ryu10/sbc6802/graphics/sbc6802r2-a.png

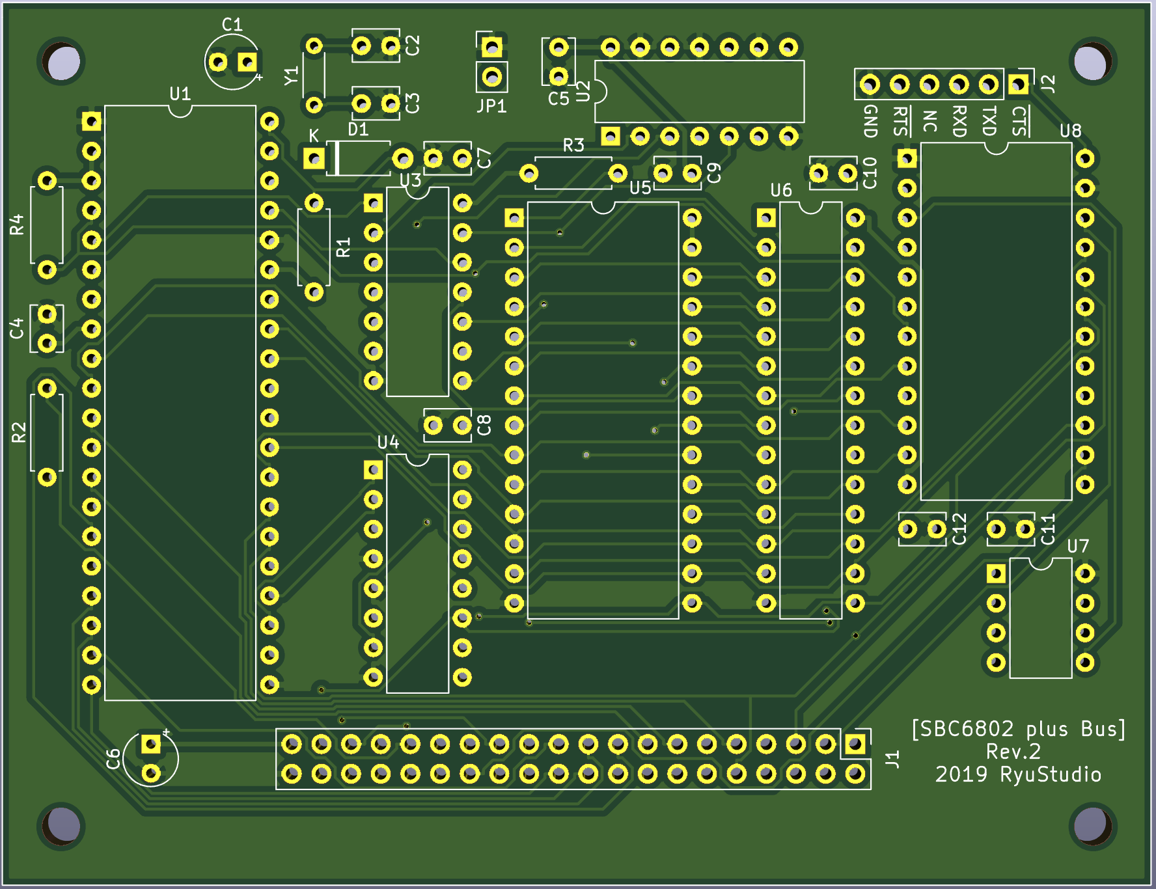
graphics/sbc6802r2-a.png
