ryu10/sbc6802/graphics/sbc6802r2-b.png

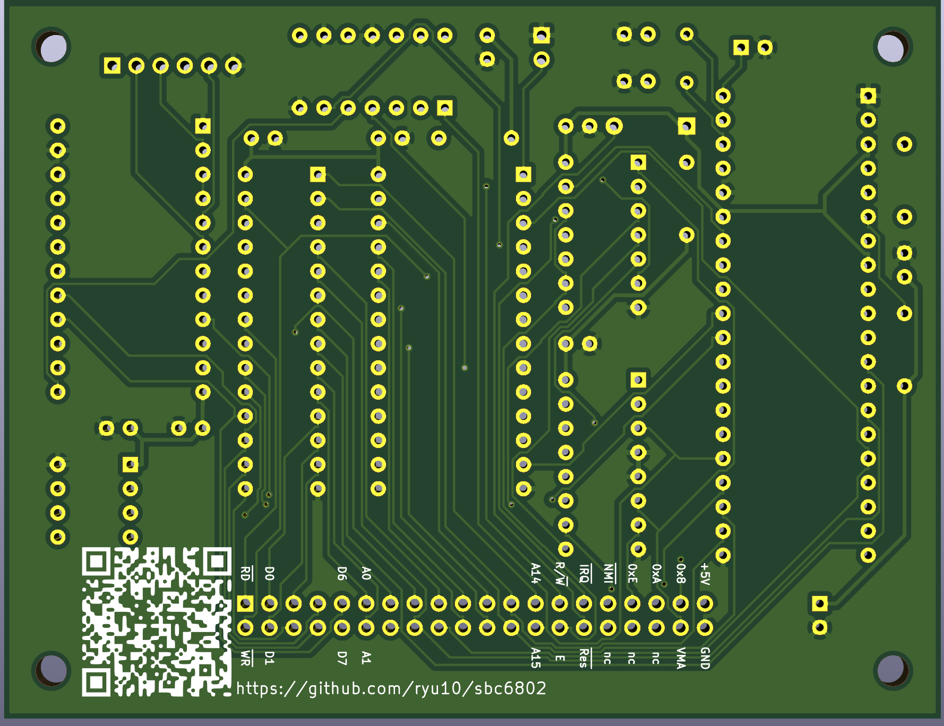
graphics/sbc6802r2-b.png
