ryu10/sbc6802/KiCAD/graphics/sbc6802board1.png

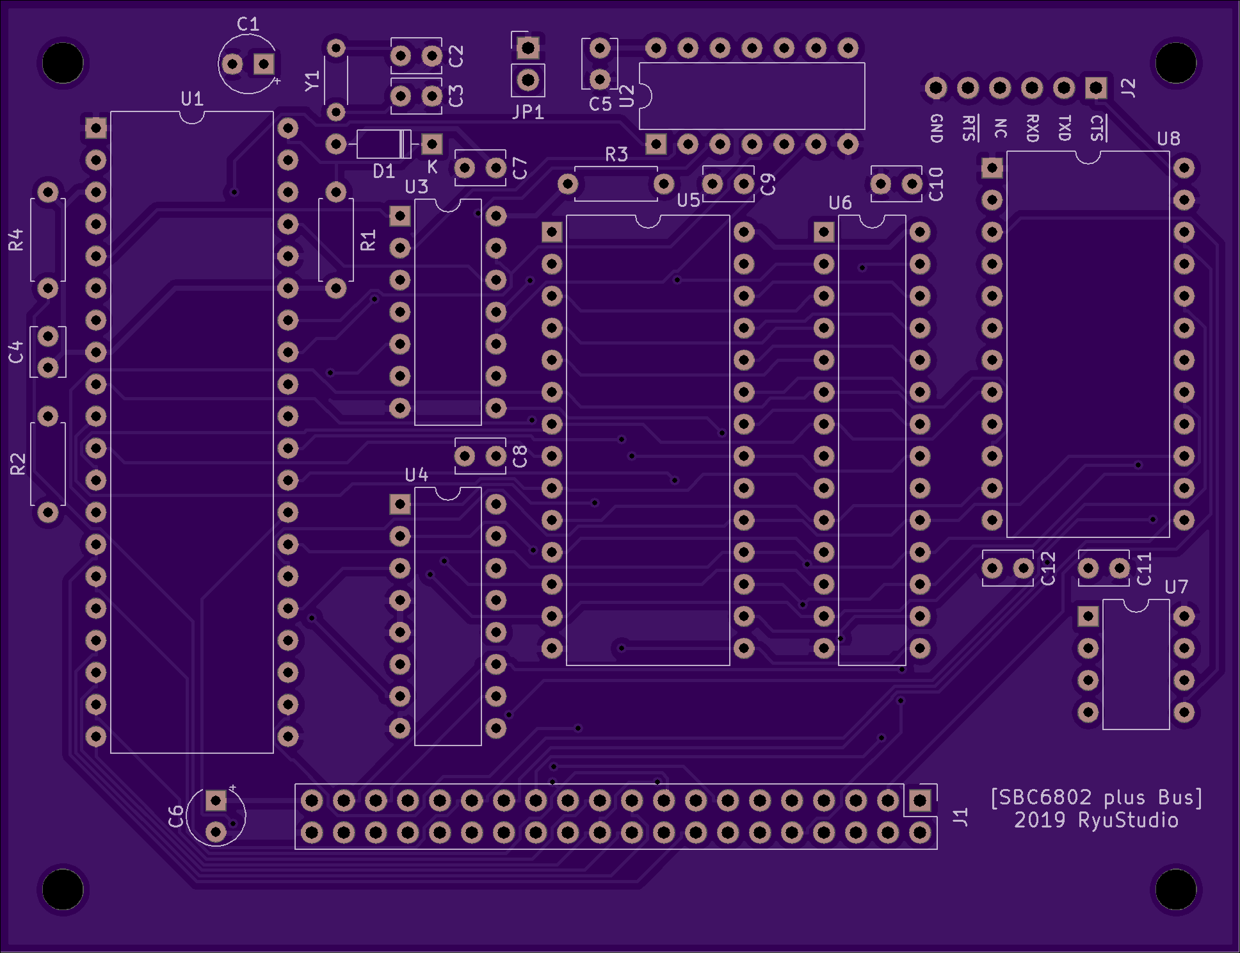
KiCAD/graphics/sbc6802board1.png
