ryu10/sbc6802/KiCAD/graphics/sbc6802board12a.png

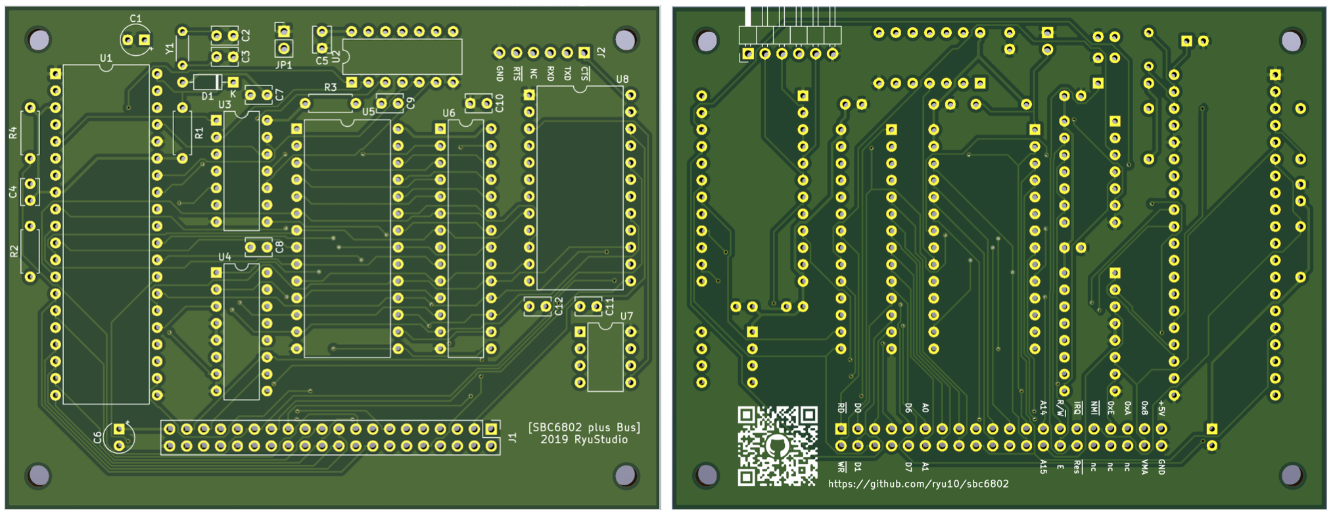
KiCAD/graphics/sbc6802board12a.png
